ThePurox/Choeradodis/choeradodis.kicad_sch

## KiCad design choeradodis.kicad_sch (2024-11-22)

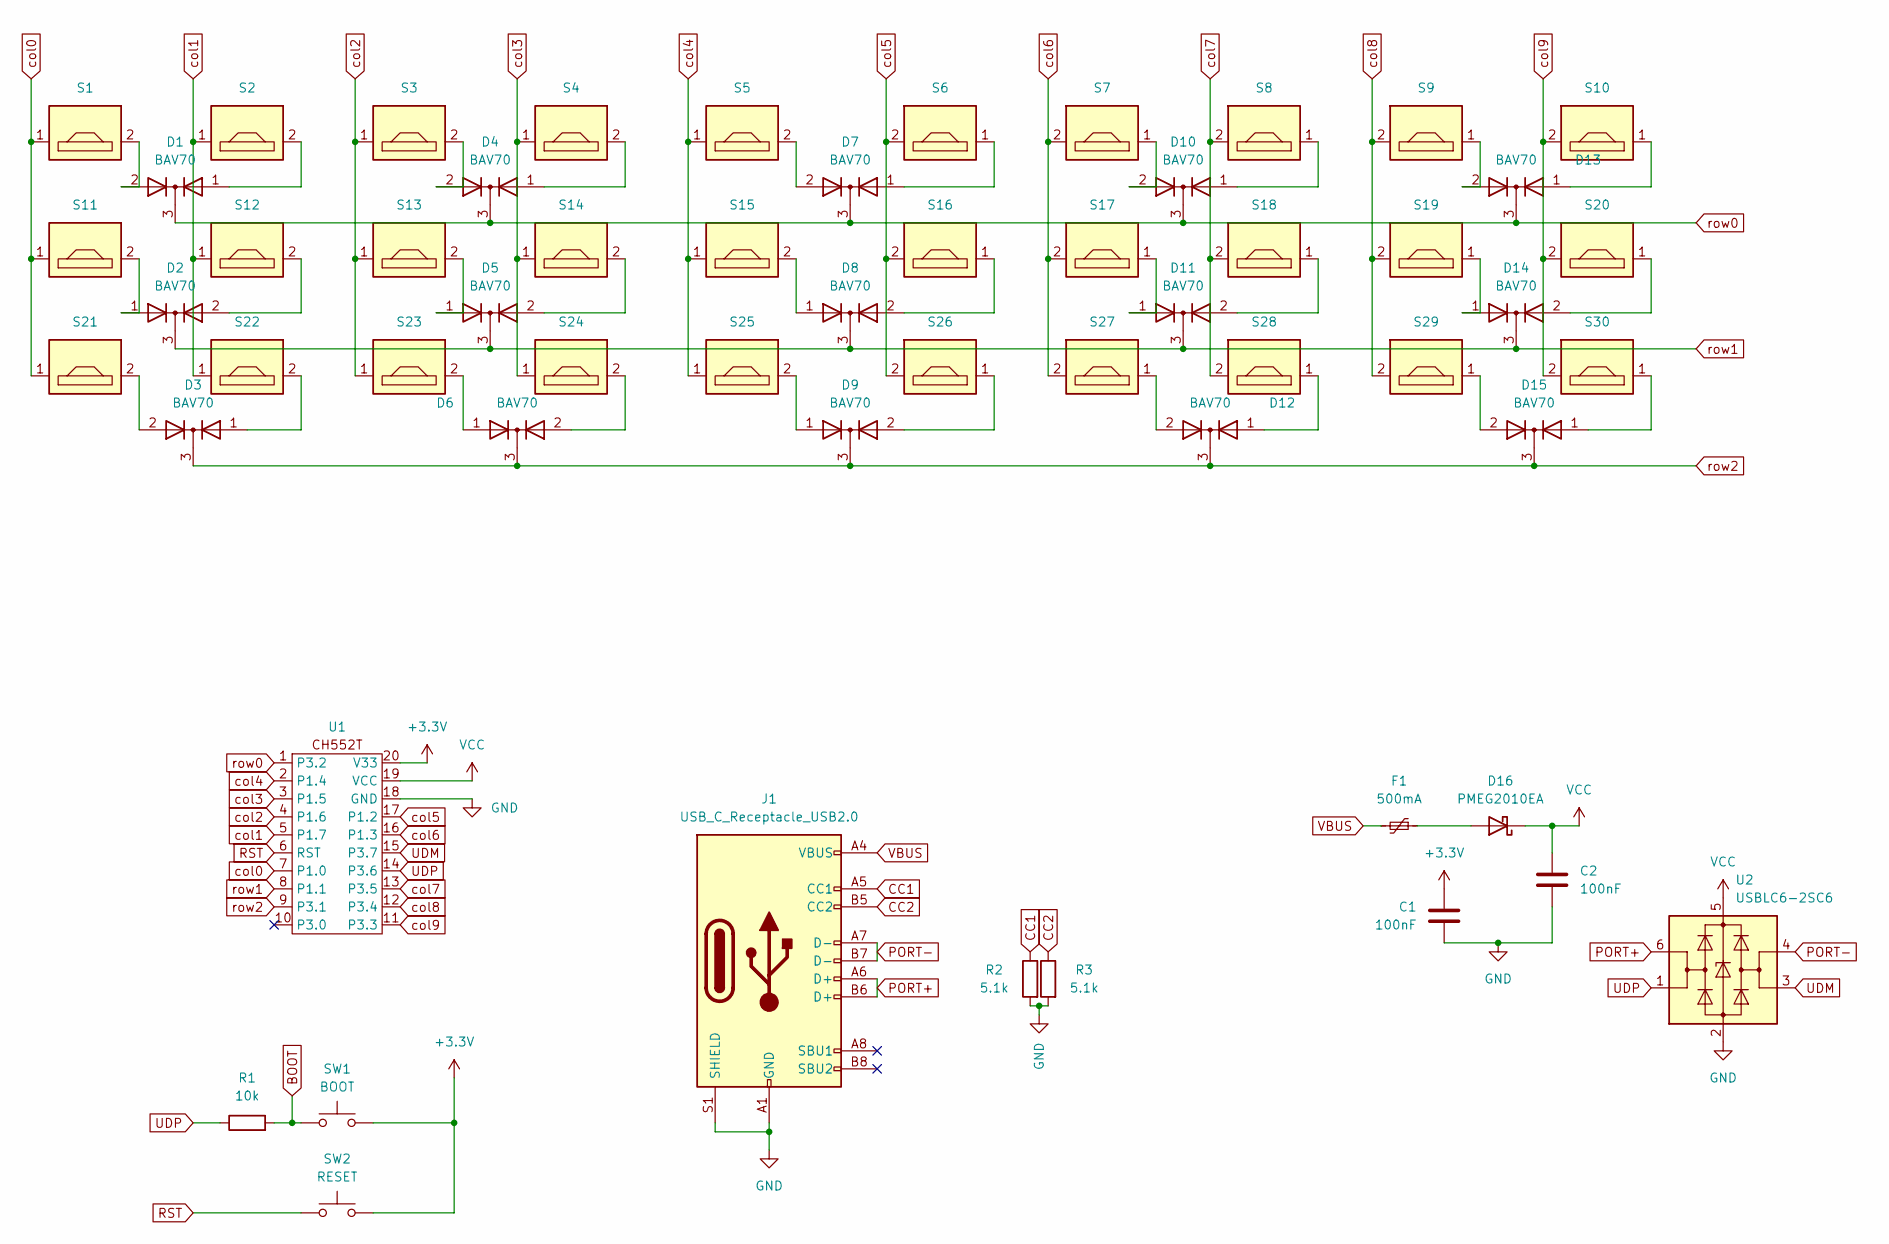
[picture p6: schematic choeradodis.kicad_sch]

Parts:
C1, C2: 100nF; C_0603_1608Metric_Pad1.08x0.95mm_HandSolder
D1, D2, D3, D4, D5, D6, D7, D8, D9, D10, D11, D12, D13, D14, D15: BAV70; SOT-23
D16: PMEG2010EA; D_SOD-323_HandSoldering
F1: 500mA; Fuse_0603_1608Metric_Pad1.05x0.95mm_HandSolder
J1: USB_C_Receptacle_USB2.0; USB_C_Receptacle_HRO_TYPE-C-31-M-12
R1: 10k; R_0603_1608Metric_Pad0.98x0.95mm_HandSolder
R2, R3: 5.1k; R_0603_1608Metric_Pad0.98x0.95mm_HandSolder
S1, S2, S3, S4, S5, S6, S7, S8, S9, S10, S11, S12, S13, S14, S15, S16, S17, S18, S19, S20, S21, S22, S23, S24, S25, S26, S27, S28, S29, S30: PG1350; Cherry_ULP_TH_CUT
SW1: BOOT; SW_Push_SPST_NO_Alps_SKRK
SW2: RESET; SW_Push_SPST_NO_Alps_SKRK
U1: TSSOP-20_4.4x6.5mm_P0.65mm
U2: USBLC6-2SC6; SOT-23-6

Connections:
+3.3V: C1.1, SW1.2, SW2.2, U1.20 (V33)
BOOT: R1.2, SW1.1
CC1: J1.A5 (CC1), R2.1
CC2: J1.B5 (CC2), R3.1
GND: C1.2, C2.2, J1.A1 (GND), J1.A12 (GND), J1.B1 (GND), J1.B12 (GND), J1.S1 (SHIELD), R2.2, R3.2, U1.18 (GND), U2.2 (GND)
unnamed: D1.1 (A), S2.2
unnamed: D1.2 (A), S1.2
unnamed: D2.1 (A), S11.2
unnamed: D2.2 (A), S12.2
unnamed: D3.1 (A), S22.2
unnamed: D3.2 (A), S21.2
unnamed: D4.1 (A), S4.2
unnamed: D4.2 (A), S3.2
unnamed: D5.1 (A), S13.2
unnamed: D5.2 (A), S14.2
unnamed: D6.1 (A), S23.2
unnamed: D6.2 (A), S24.2
unnamed: D7.1 (A), S6.1
unnamed: D7.2 (A), S5.2
unnamed: D8.1 (A), S15.2
unnamed: D8.2 (A), S16.1
unnamed: D9.1 (A), S25.2
unnamed: D9.2 (A), S26.1
unnamed: D10.1 (A), S8.1
unnamed: D10.2 (A), S7.1
unnamed: D11.1 (A), S17.1
unnamed: D11.2 (A), S18.1
unnamed: D12.1 (A), S28.1
unnamed: D12.2 (A), S27.1
unnamed: D13.1 (A), S10.1
unnamed: D13.2 (A), S9.1
unnamed: D14.1 (A), S19.1
unnamed: D14.2 (A), S20.1
unnamed: D15.1 (A), S30.1
unnamed: D15.2 (A), S29.1
unnamed: D16.2 (A), F1.1
PORT+: J1.A6 (D+), J1.B6 (D+), U2.6 (I/O1)
PORT-: J1.A7 (D-), J1.B7 (D-), U2.4 (I/O2)
RST: SW2.1, U1.6 (RST)
UDM: U1.15 (P3.7), U2.3 (I/O2)
UDP: R1.1, U1.14 (P3.6), U2.1 (I/O1)
VBUS: F1.2, J1.A4 (VBUS), J1.A9 (VBUS), J1.B4 (VBUS), J1.B9 (VBUS)
VCC: C2.1, D16.1 (K), U1.19 (VCC), U2.5 (VBUS)
col0: S1.1, S11.1, S21.1, U1.7 (P1.0)
col1: S2.1, S12.1, S22.1, U1.5 (P1.7)
col2: S3.1, S13.1, S23.1, U1.4 (P1.6)
col3: S4.1, S14.1, S24.1, U1.3 (P1.5)
col4: S5.1, S15.1, S25.1, U1.2 (P1.4)
col5: S6.2, S16.2, S26.2, U1.17 (P1.2)
col6: S7.2, S17.2, S27.2, U1.16 (P1.3)
col7: S8.2, S18.2, S28.2, U1.13 (P3.5)
col8: S9.2, S19.2, S29.2, U1.12 (P3.4)
col9: S10.2, S20.2, S30.2, U1.11 (P3.3)
row0: D1.3 (K), D4.3 (K), D7.3 (K), D10.3 (K), D13.3 (K), U1.1 (P3.2)
row1: D2.3 (K), D5.3 (K), D8.3 (K), D11.3 (K), D14.3 (K), U1.8 (P1.1)
row2: D3.3 (K), D6.3 (K), D9.3 (K), D12.3 (K), D15.3 (K), U1.9 (P3.1)
